GustavoSantiago113/Estacao-Meteorologica/3D_Structure/Protetor temp e umi/Rad_Shd_Fin_V1.stl

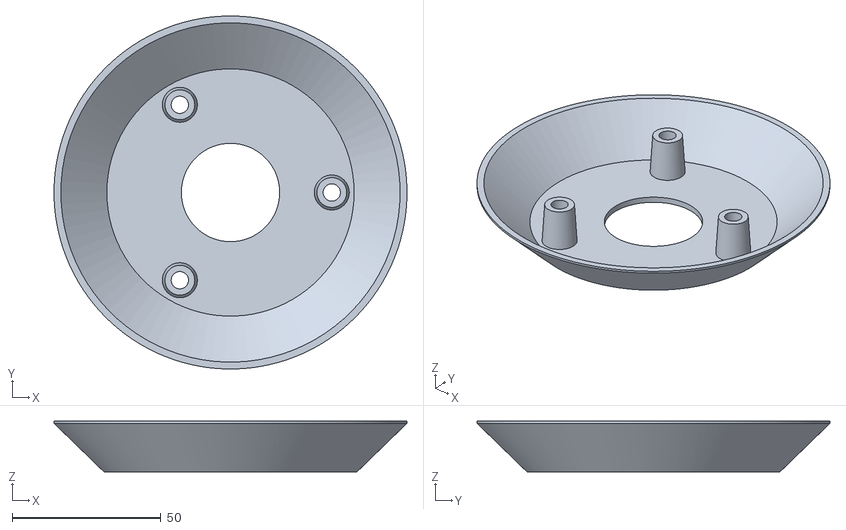
[picture p18: CAD file, 2022-09-23]
3D_Structure/Protetor temp e umi/Rad_Shd_Fin_V1.stl
118.5 x 118.5 x 17.0
