GustavoSantiago113/Estacao-Meteorologica/3D_Structure/Pluviômetro/Bending_tool.stl

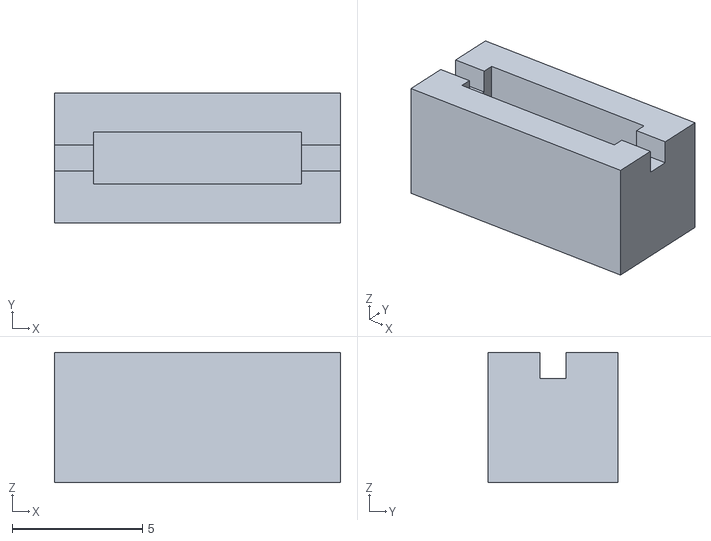
[picture p19: CAD file, 2022-09-23]
3D_Structure/Pluviômetro/Bending_tool.stl
11.0 x 5.00 x 5.00
