GustavoSantiago113/Estacao-Meteorologica/3D_Structure/Protetor temp e umi/Rad_Shd_Horz_mount_V1.stl

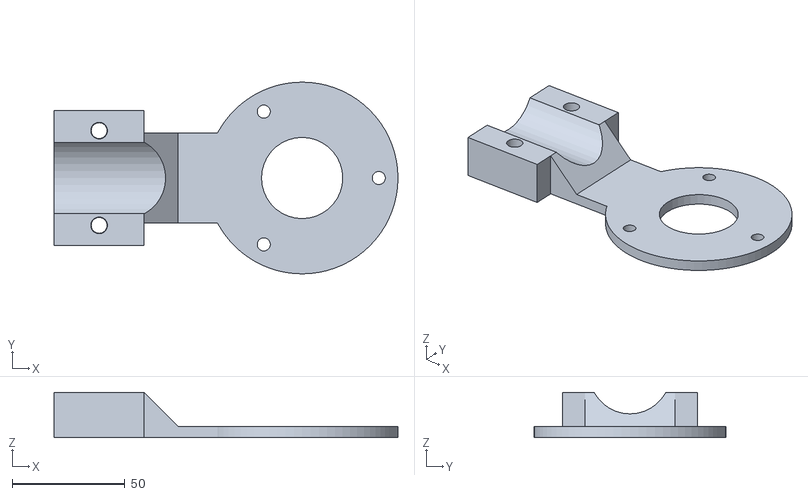
[picture p20: CAD file, 2022-09-23]
3D_Structure/Protetor temp e umi/Rad_Shd_Horz_mount_V1.stl
152.5 x 85.0 x 20.0
