GustavoSantiago113/Estacao-Meteorologica/3D_Structure/Pluviômetro/Bucket.stl

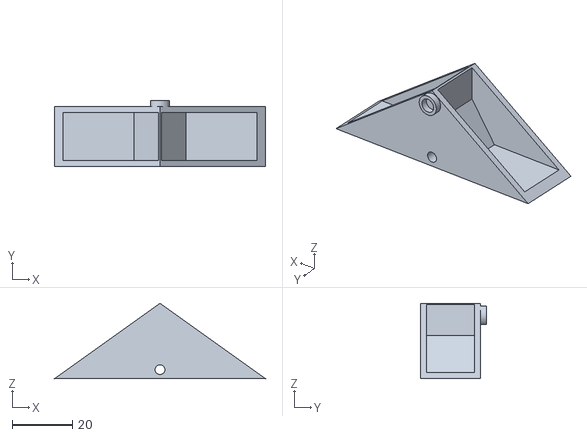
[picture p21: CAD file, 2022-09-23]
3D_Structure/Pluviômetro/Bucket.stl
70.0 x 22.0 x 25.0
